yoonseo-choi/ece445_fa22/notebooks/sean/version1_pcb.png

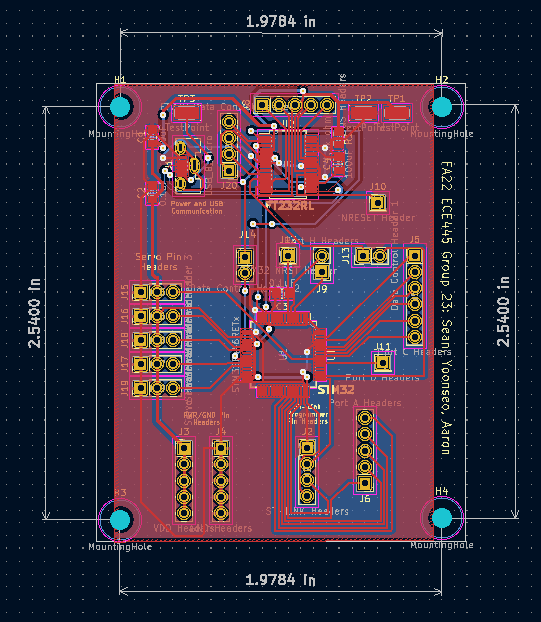
notebooks/sean/version1_pcb.png
