yoonseo-choi/ece445_fa22/notebooks/sean/version2_pcb.png

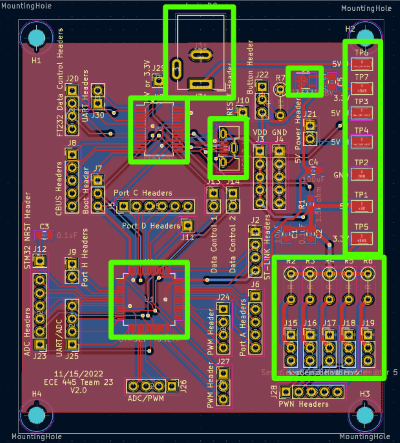
notebooks/sean/version2_pcb.png
